1stage/Aquarius-MX/img/aq-mx-github-qr.png

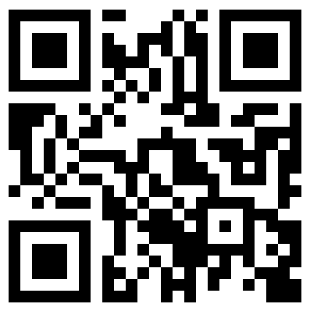
img/aq-mx-github-qr.png
