1stage/Aquarius-MX/img/aq_mx_chip_labels.jpg

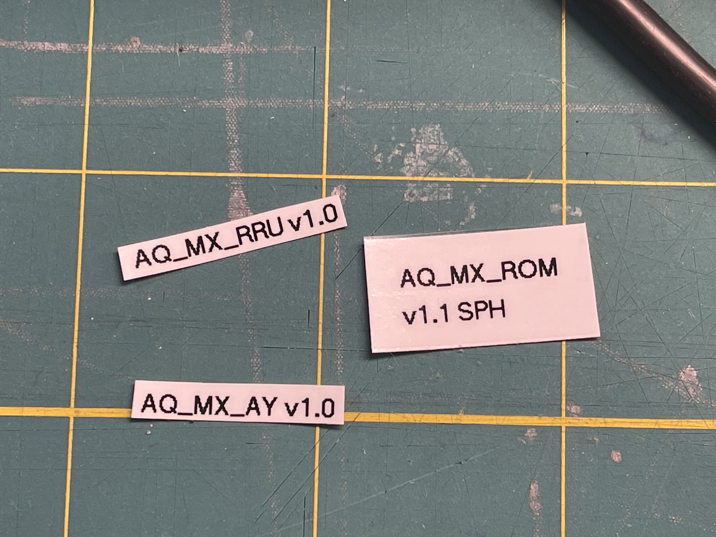
img/aq_mx_chip_labels.jpg
