1stage/Aquarius-MX/img/aq_mx_chip_prog.jpg

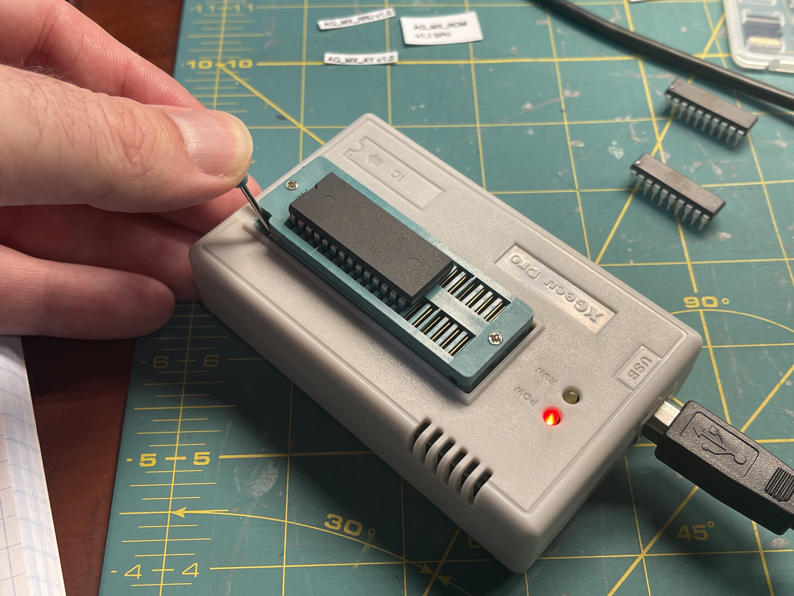
img/aq_mx_chip_prog.jpg
