1stage/Aquarius-MX/img/aq_mx_label.jpg

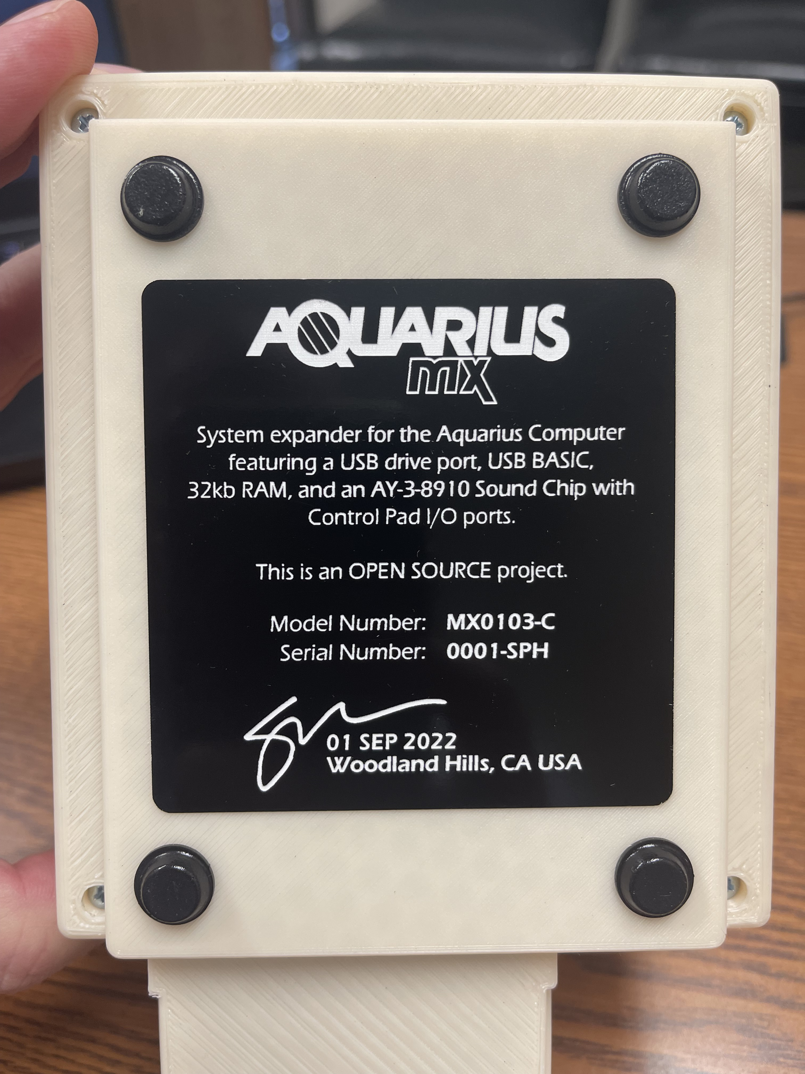
img/aq_mx_label.jpg
