1stage/Aquarius-MX/img/aq_mx_pcb.jpg

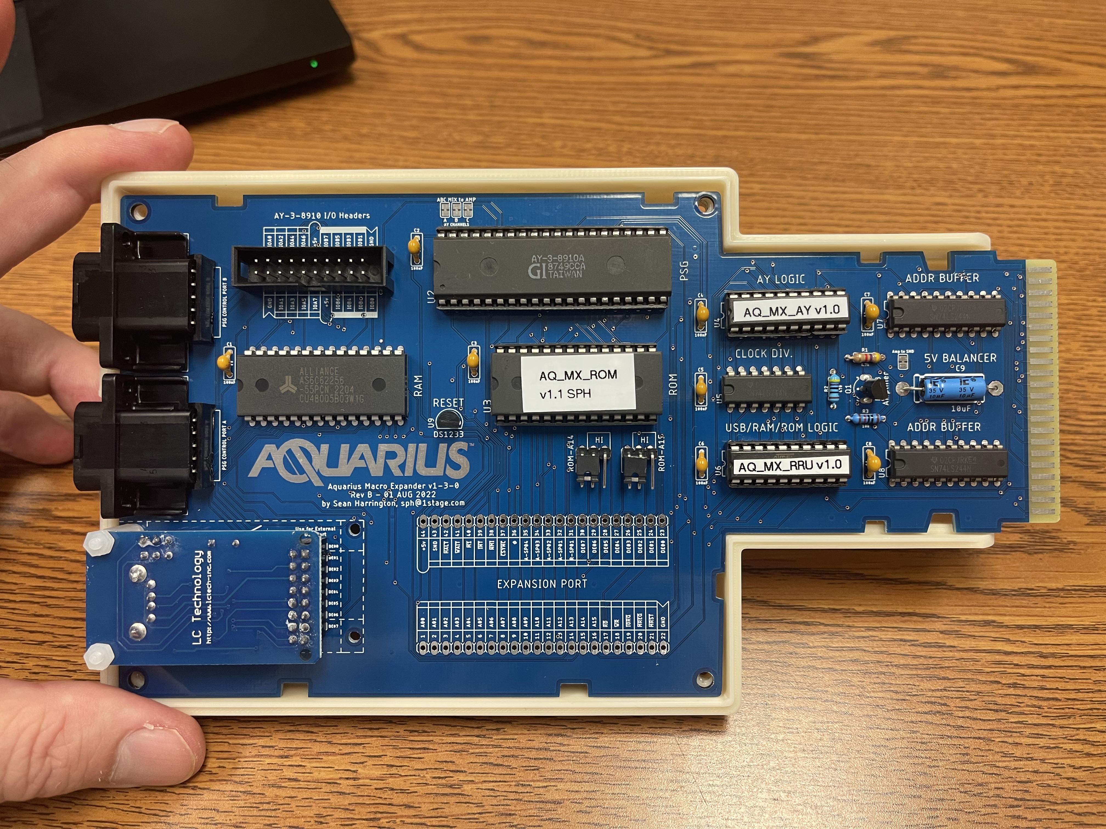
img/aq_mx_pcb.jpg
