1stage/Aquarius-MX/img/aq_mx_side.jpg

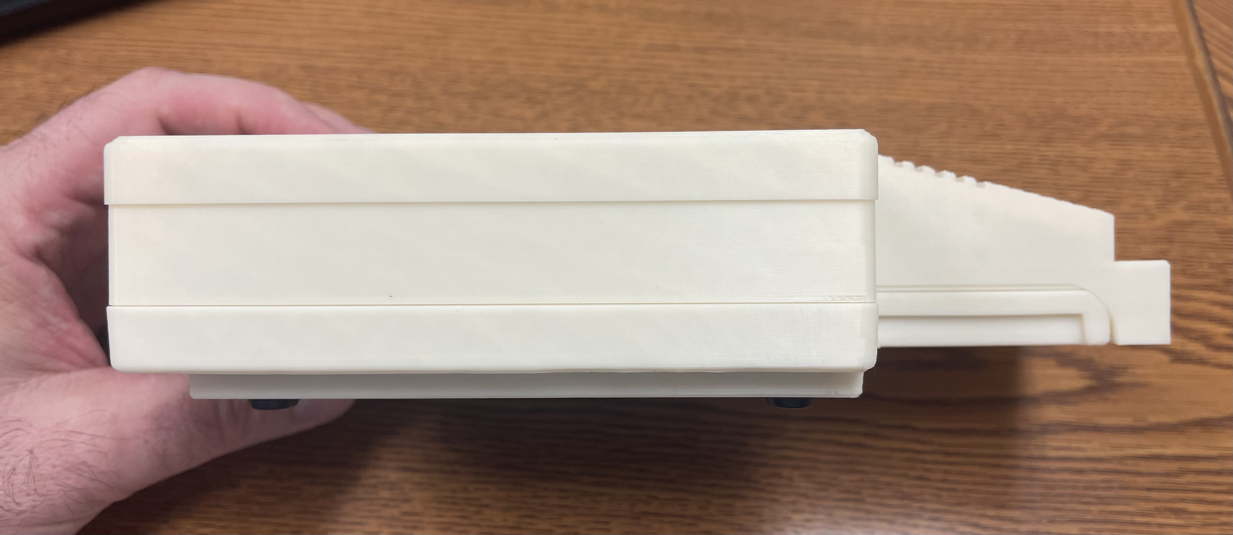
img/aq_mx_side.jpg
