1stage/Aquarius-MX/src/rom/textpad zmac.png

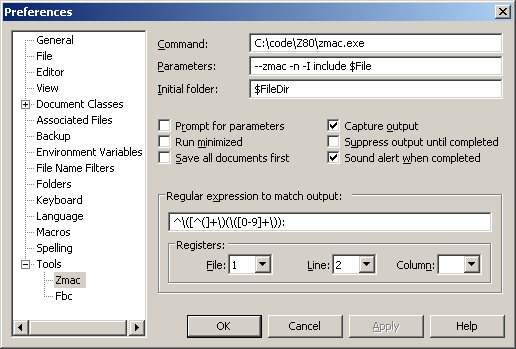
src/rom/textpad zmac.png
