1stage/Aquarius-MX/docs/aq_mx_v1-3-0c_BOARD.pdf

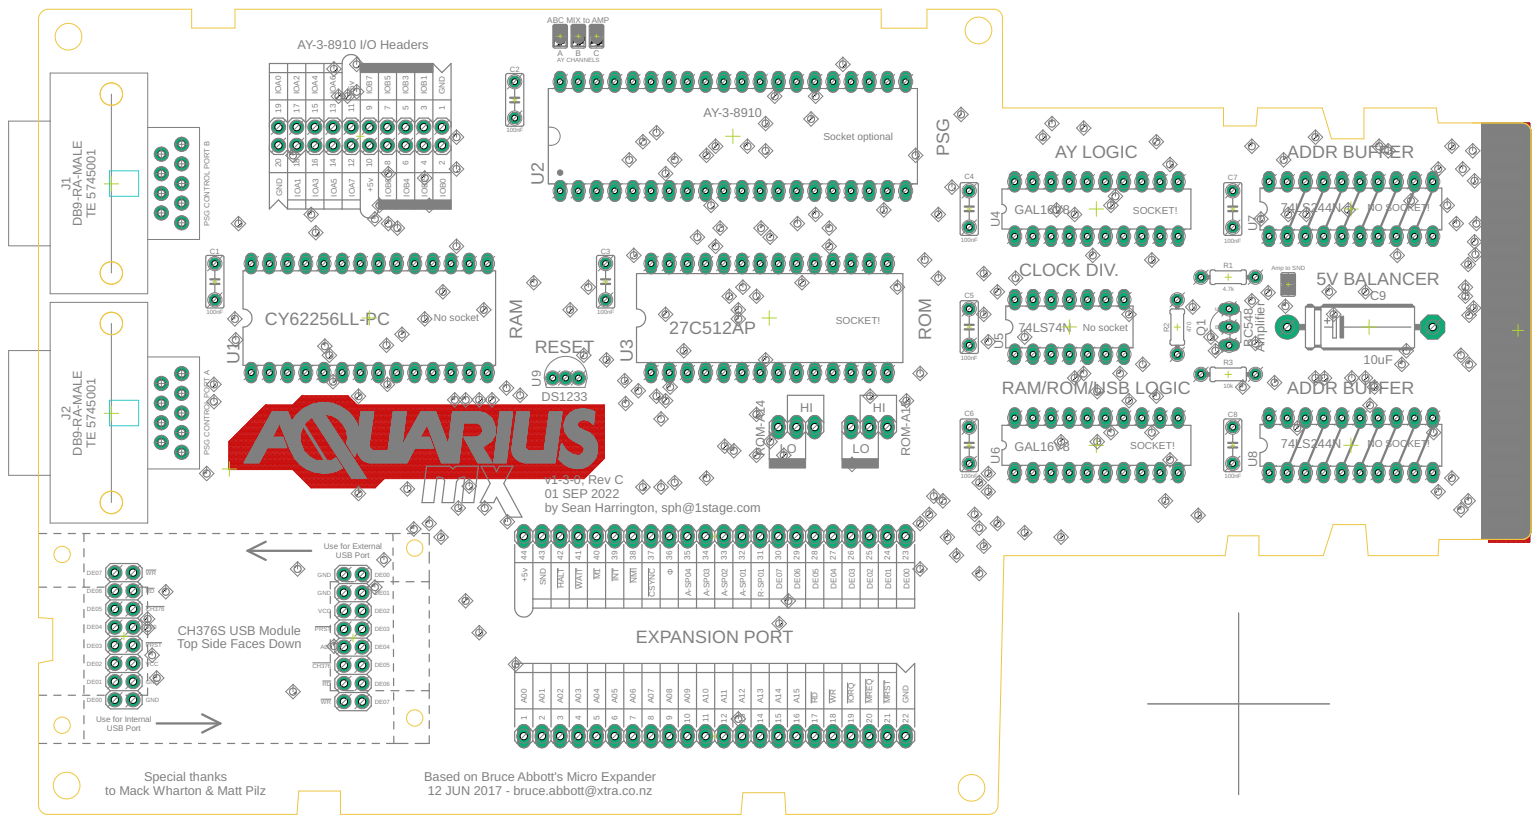
[picture p28: page 1]

ABC MIX to AMP

PSG CONTROL PORT B PSG CONTROL PORT A

No socket

RAM/ROM/USB LOGIC

ROM-A14HI HI LO LO

v1-3-0, Rev C
01 SEP 2022
by Sean Harrington, sph@1stage.com

CH376S USB Module Top Side Faces Down

IORQ 19 MREQ 20 MRST 21 GND 22

Based on Bruce Abbott's Micro Expander 12 JUN 2017 - bruce.abbott@xtra.co.nz

to Mack Wharton & Matt Pilz
